KarlZeilhofer/gamearino/3d/steuerkreuz-zeik/steuerkreuz_zeik.pdf

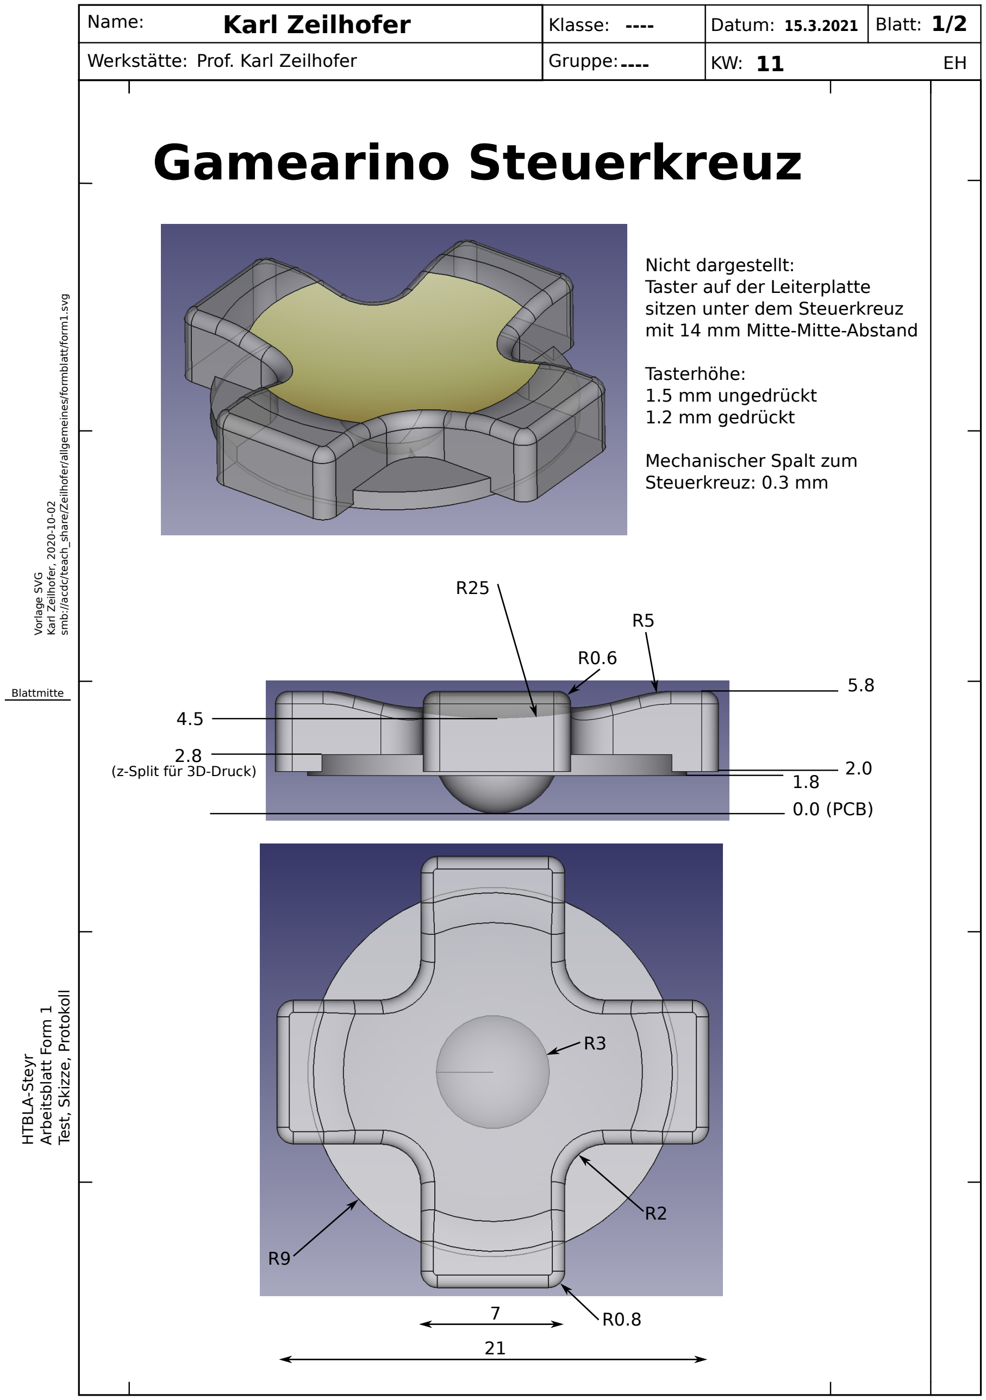
[picture p2: figure]
Werkstätte: Prof. Karl Zeilhofer; Gruppe: ----; HTBLA-Steyr; Arbeitsblatt Form 1; Test, Skizze, Protokoll; Vorlage SVG; Karl Zeilhofer, 2020-10-02; smb://acdc/teach_share/Zeilhofer/allgemeines/formblatt/form1.svg; Blattmitte; Gamearino Steuerkreuz; 0.0 (PCB); (z-Split für 3D-Druck); Nicht dargestellt: Taster auf der Leiterplatte sitzen unter dem Steuerkreuz mit 14 mm Mitte-Mitte-Abstand; Tasterhöhe: 1.5 mm ungedrückt 1.2 mm gedrückt; Mechanischer Spalt zum Steuerkreuz: 0.3 mm

Name: Karl Zeilhofer | Klasse: ---- | Datum: 15.3.2021 | 1/2 Blatt:

Name: Karl Zeilhofer | Klasse: ---- | Datum: 15.3.2021 | 2/2 Blatt:
Werkstätte: Prof. Karl Zeilhofer | Gruppe: ---- | KW: 11 EH

HTBLA-Steyr

Arbeitsblatt Form 1

Test, Skizze, Protokoll

Vorlage SVG

Karl Zeilhofer, 2020-10-02 smb://acdc/teach_share/Zeilhofer/allgemeines/formblatt/form1.svg

Blattmitte

# 3D-Druck des Steuerkreuzes

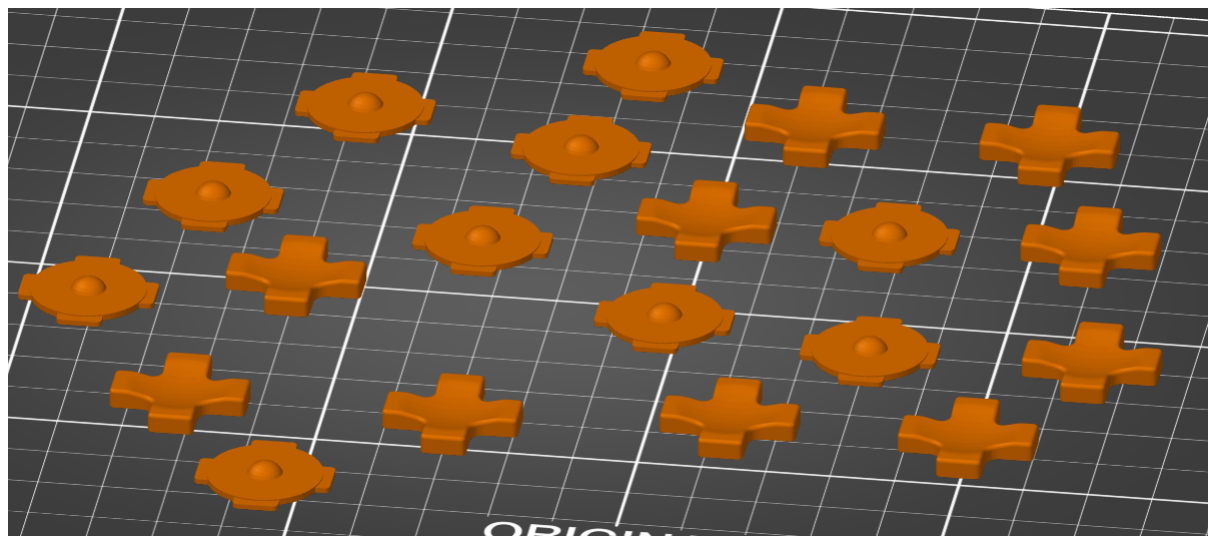
[picture p3: figure]

Das 3D-Modell wird auf Höhe 2.8 mm geteilt, um Stützstrukturen zu vermeiden, und somit saubere Oberflächen unten wie oben zu ermöglichen. Durch das Drucken vieler Teile gleichzeitig erreicht man eine bessere Qualität, da die Oberfläche der vorhergehenden Schicht Zeit bekommt, auszukühlen.

Druckmaterial: ecoPET
Drucktemperatur: 215/210 °C
Drucker: Prusa i3 MK3

Schichthöhe: 0.1 mm
