KarlZeilhofer/gamearino/3d/Screenshot from 2021-03-17 17-25-13.png

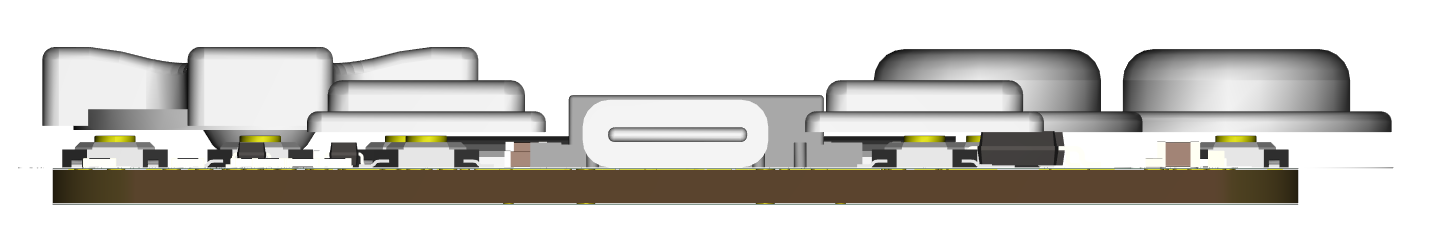
3d/Screenshot from 2021-03-17 17-25-13.png
