KarlZeilhofer/gamearino/3d/Screenshot from 2021-03-17 17-26-16.png

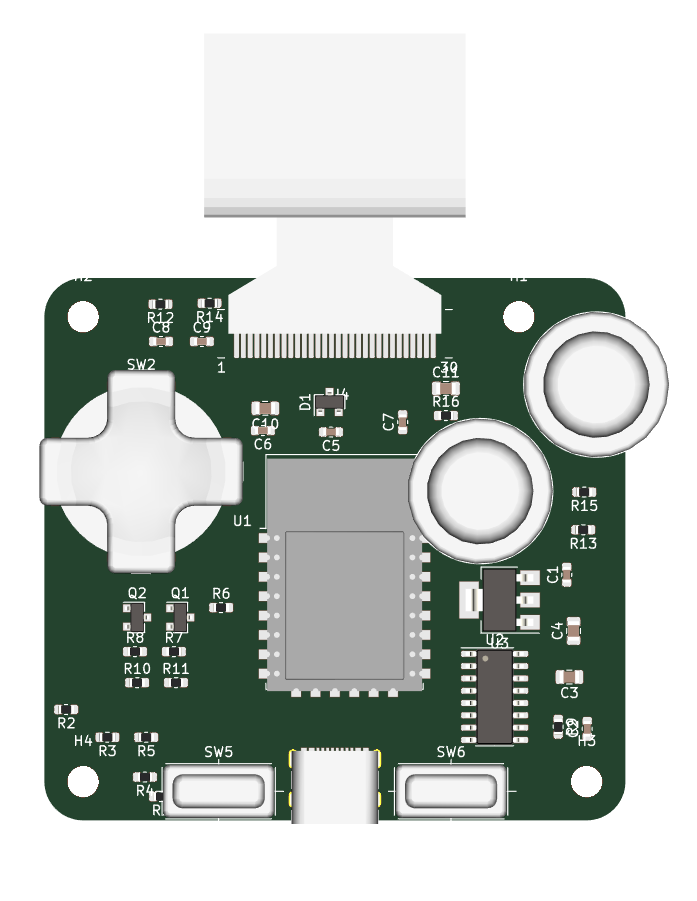
3d/Screenshot from 2021-03-17 17-26-16.png
