KarlZeilhofer/gamearino/3d/steuerkreuz-zeik/Screenshot from 2021-03-15 12-45-00.png

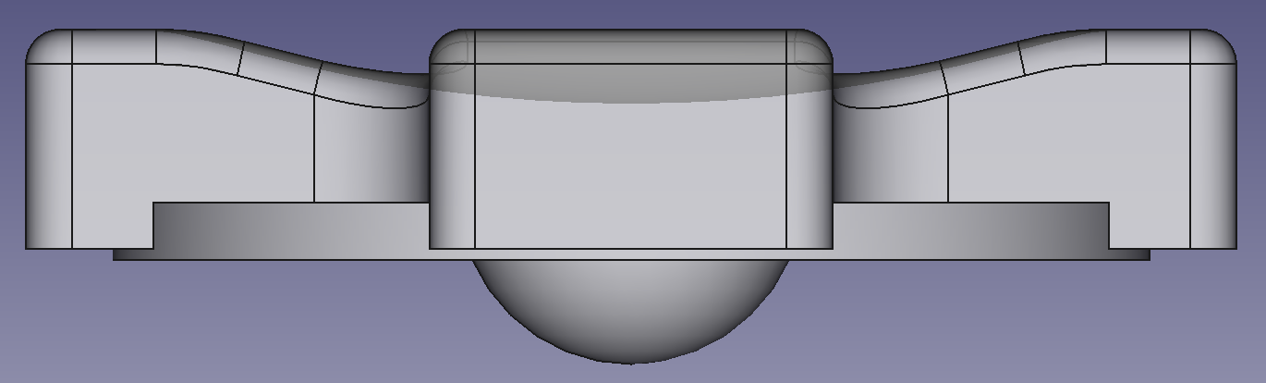
3d/steuerkreuz-zeik/Screenshot from 2021-03-15 12-45-00.png
