KarlZeilhofer/gamearino/3d/steuerkreuz-zeik/Screenshot from 2021-03-15 13-13-52.png

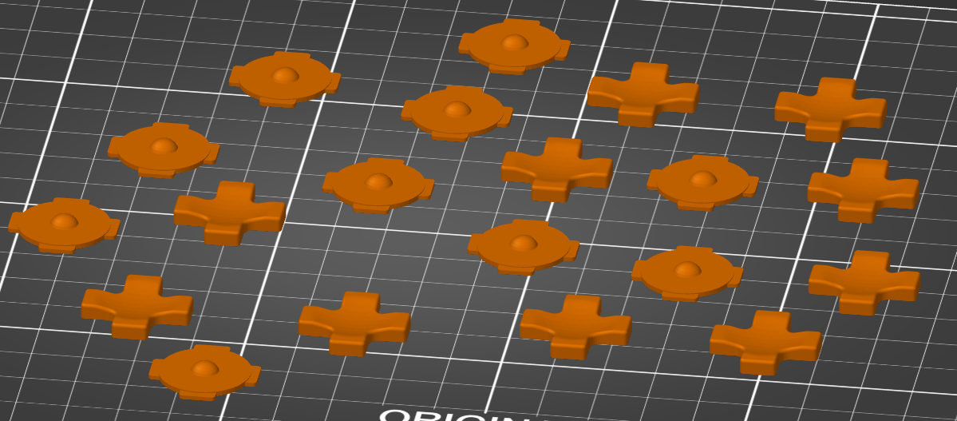
3d/steuerkreuz-zeik/Screenshot from 2021-03-15 13-13-52.png
