KarlZeilhofer/gamearino/bestellungen/2020-10-12_003.png

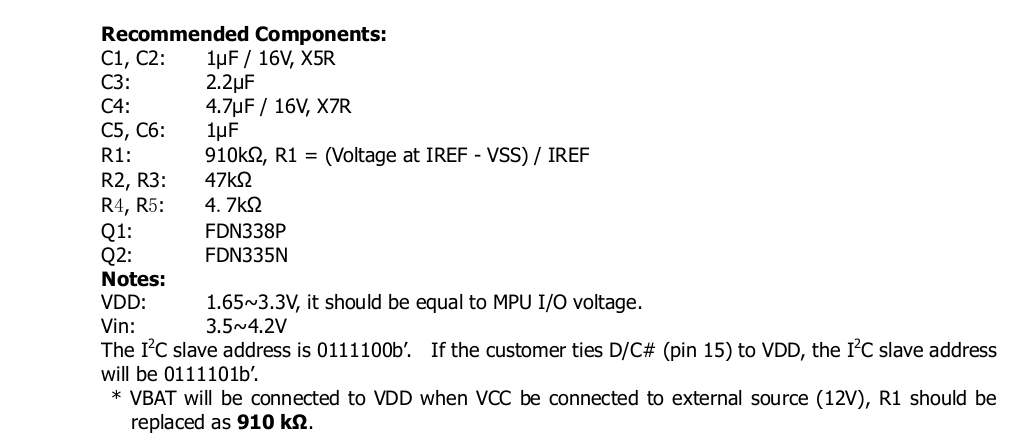
bestellungen/2020-10-12_003.png
