KarlZeilhofer/gamearino/bestellungen/2020-10-12_004.png

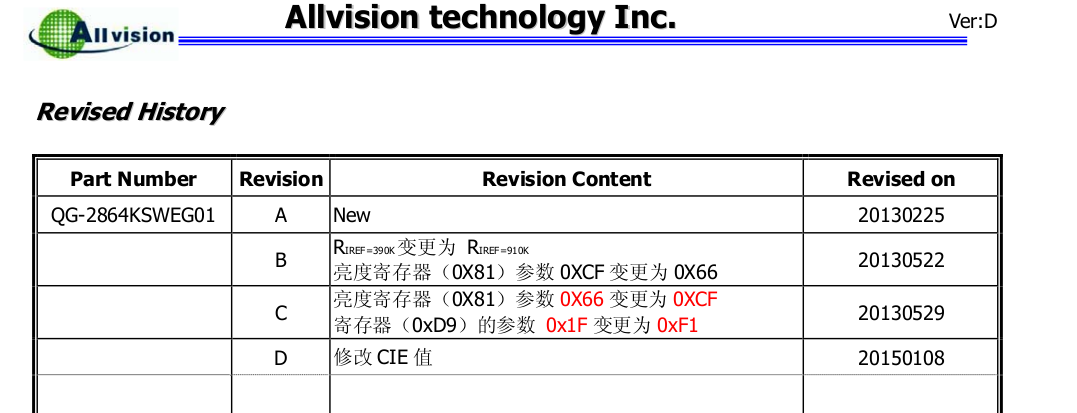
bestellungen/2020-10-12_004.png
