KarlZeilhofer/gamearino/bestellungen/2020-10-12_005.png

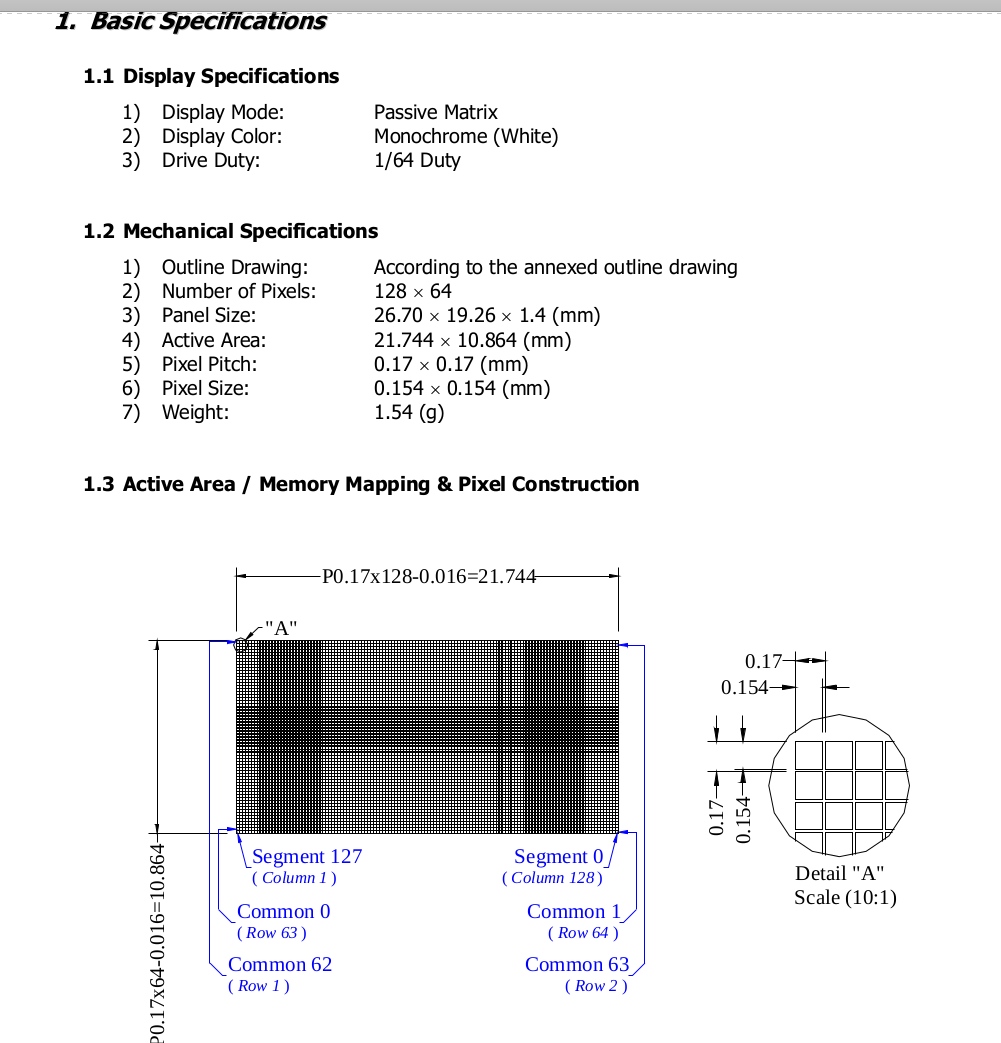
bestellungen/2020-10-12_005.png
