KarlZeilhofer/gamearino/bestellungen/2020-10-12_006.png

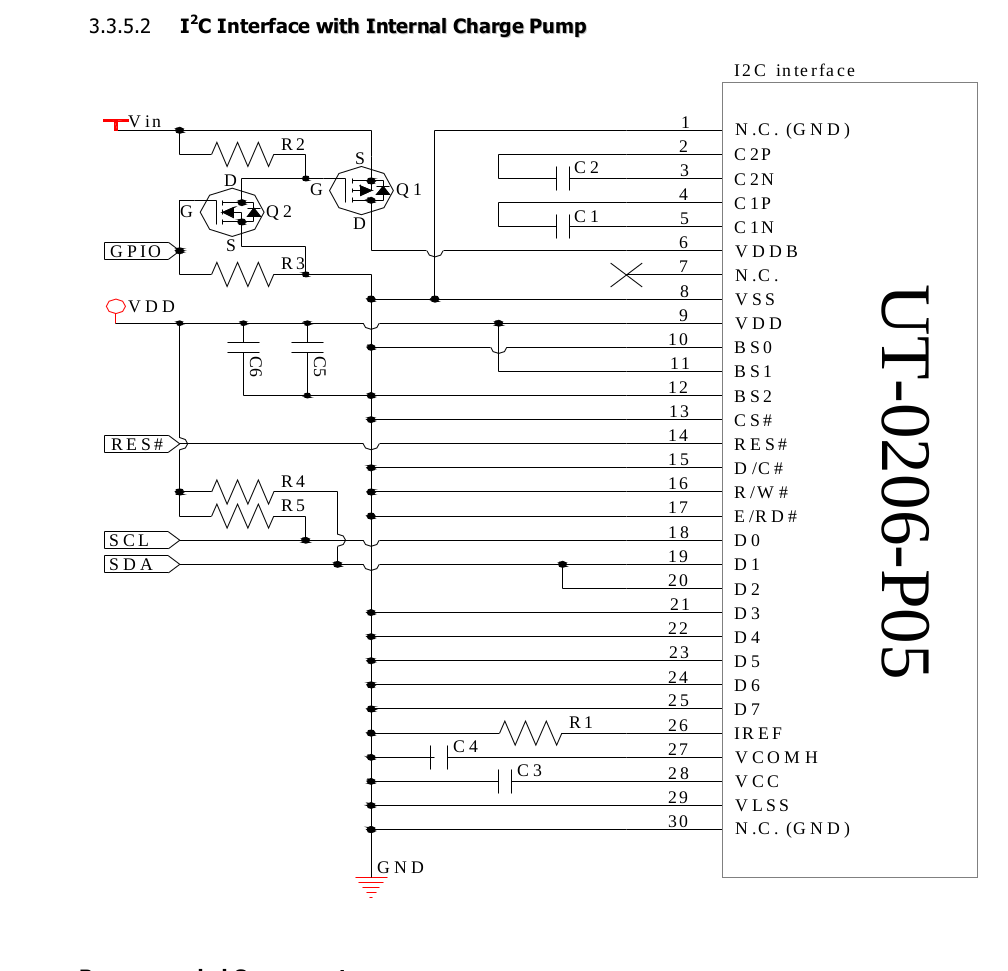
bestellungen/2020-10-12_006.png
