KarlZeilhofer/gamearino/bestellungen/2020-10-12_007.png

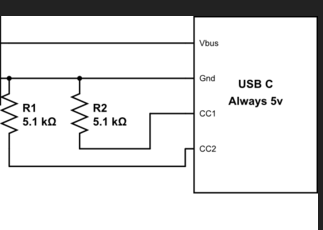
bestellungen/2020-10-12_007.png
