KarlZeilhofer/gamearino/brainstorming/2020-10-13_001.png

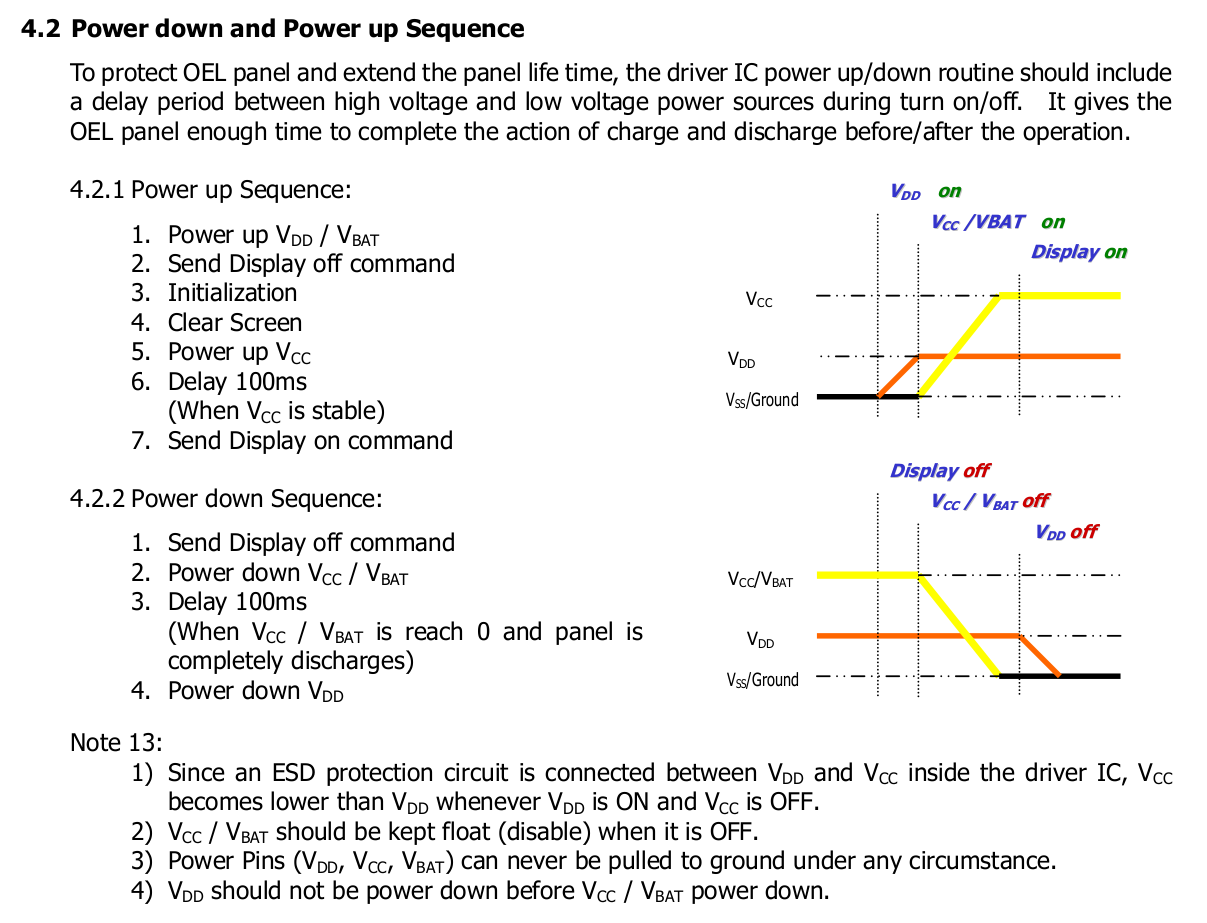
brainstorming/2020-10-13_001.png
