KarlZeilhofer/gamearino/inbetriebnahme_v0.0.2/2021-05-10_001.png

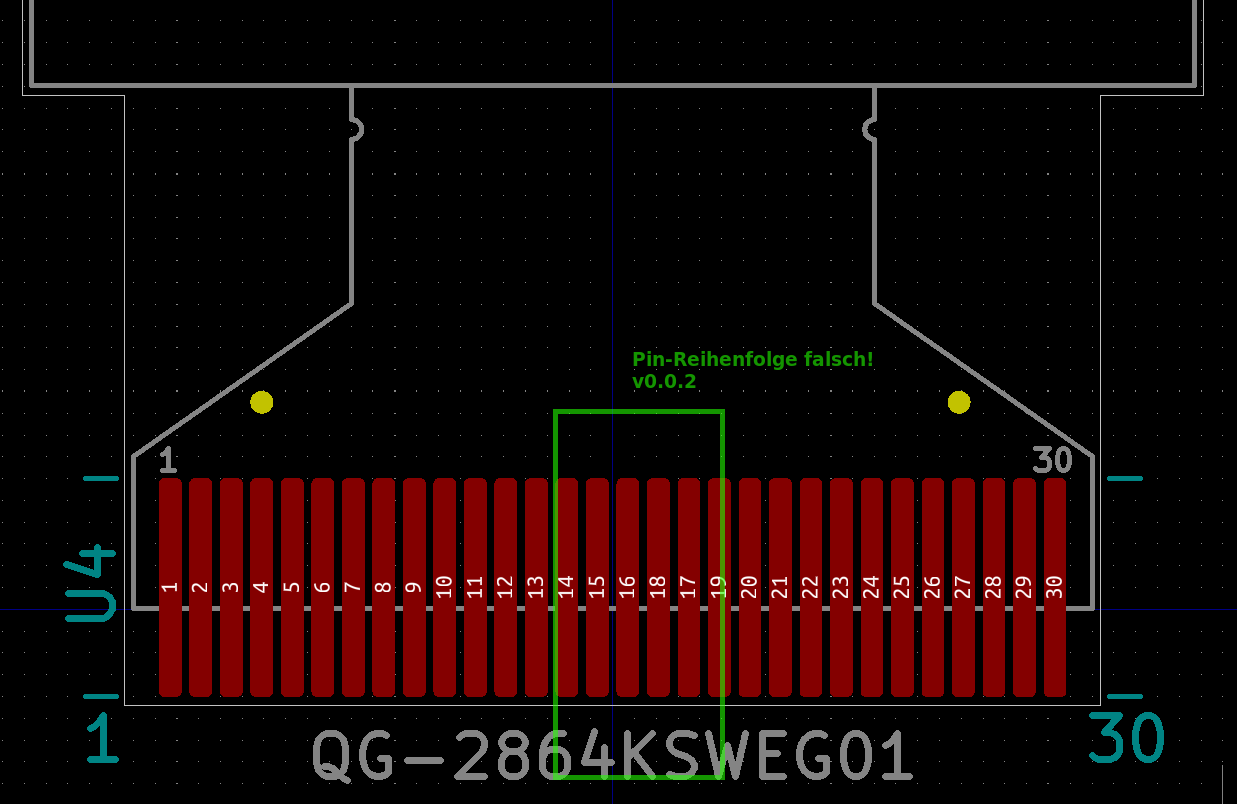
inbetriebnahme_v0.0.2/2021-05-10_001.png
