KarlZeilhofer/gamearino/kicad/screenshots/2021-04-29_012.png

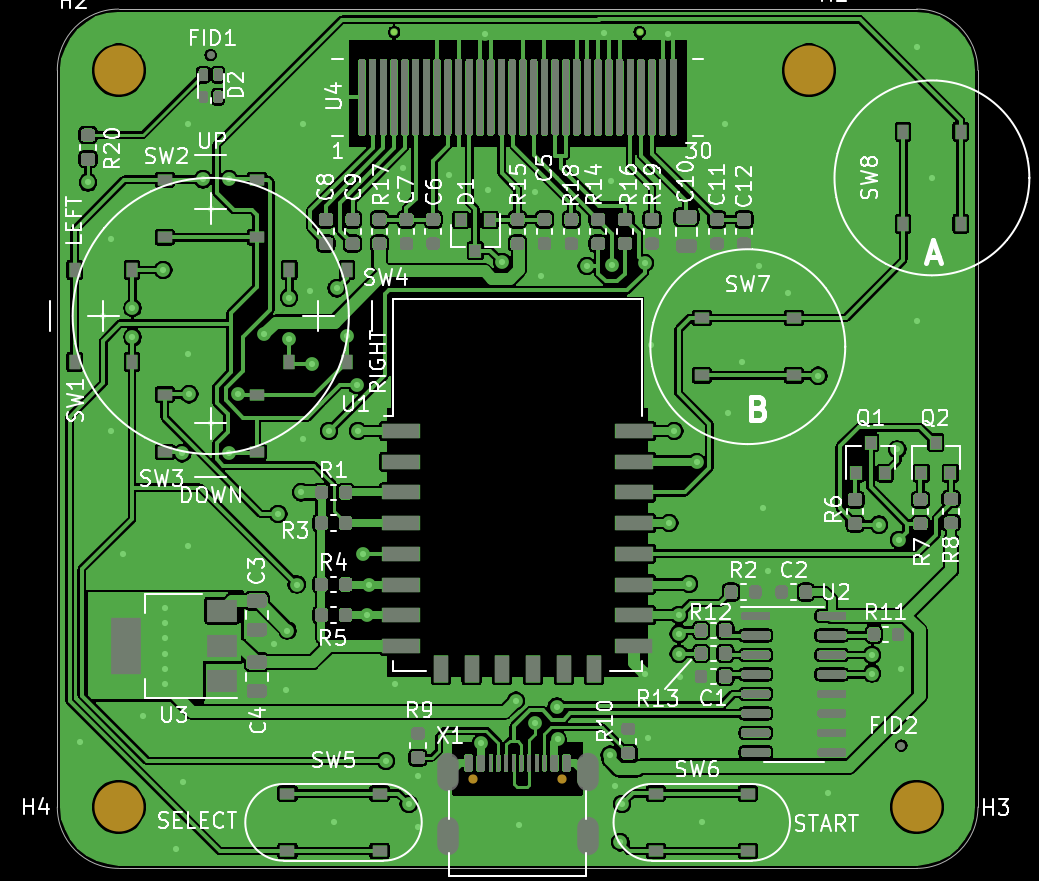
kicad/screenshots/2021-04-29_012.png
