KarlZeilhofer/gamearino/kicad/screenshots/2021-04-29_013.png

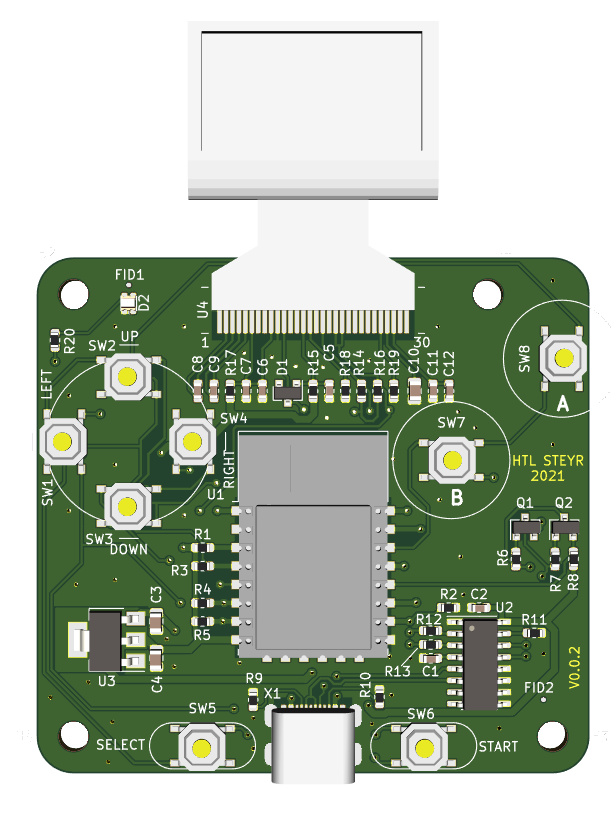
kicad/screenshots/2021-04-29_013.png
