KarlZeilhofer/gamearino/kicad/screenshots/2021-04-29_014.png

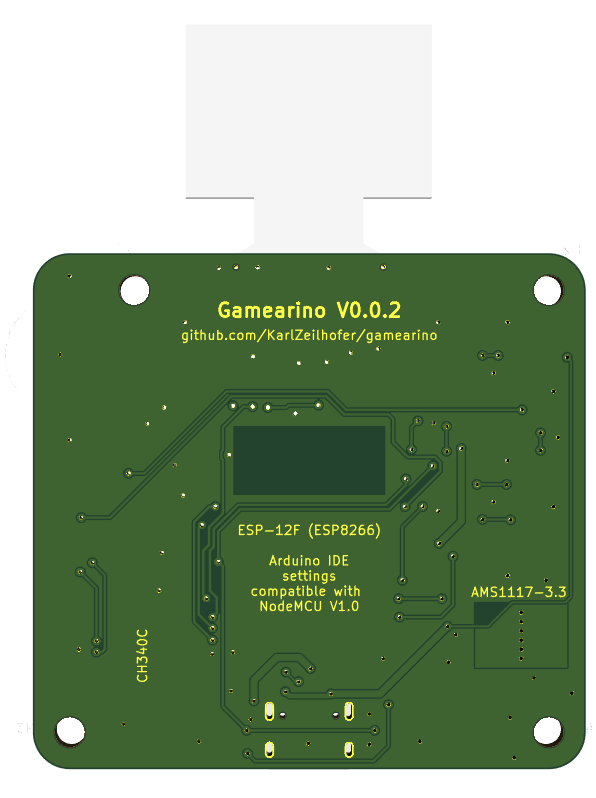
kicad/screenshots/2021-04-29_014.png
