KarlZeilhofer/gamearino/kicad/screenshots/2021-04-29_015.png

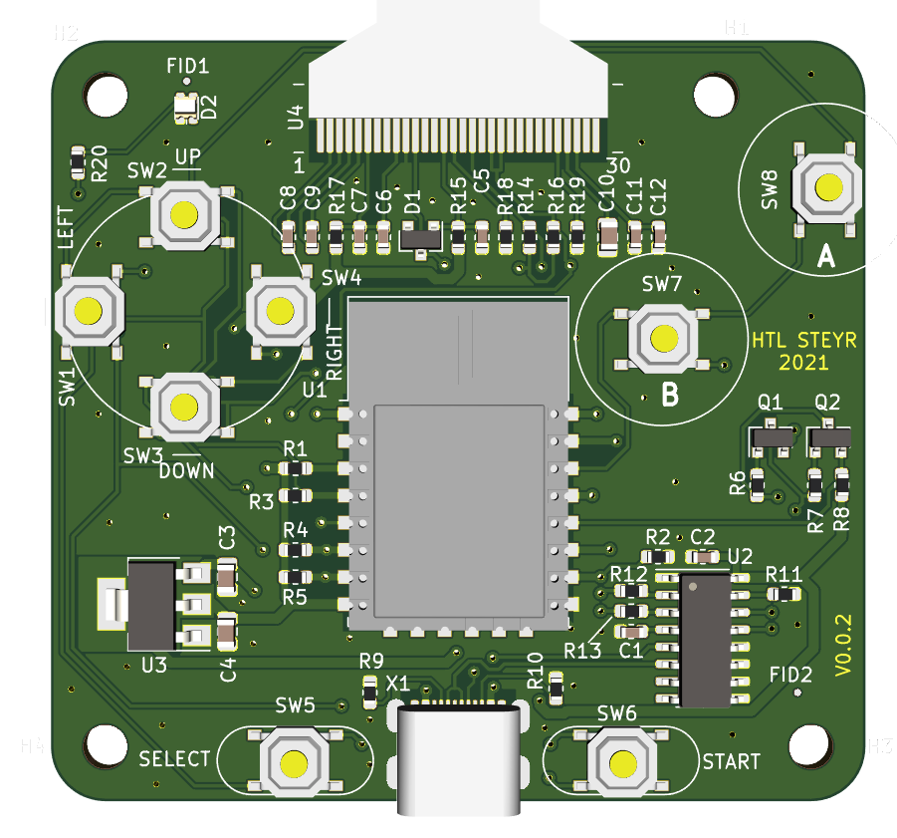
kicad/screenshots/2021-04-29_015.png
