KarlZeilhofer/gamearino/kicad/screenshots/2021-04-29_016.png

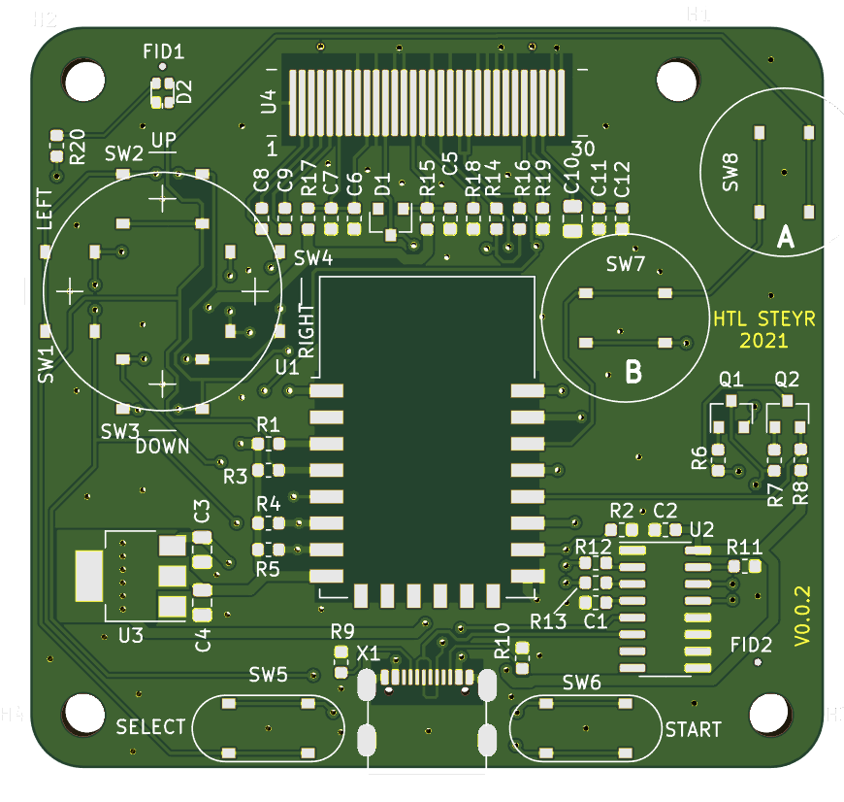
kicad/screenshots/2021-04-29_016.png
