KarlZeilhofer/gamearino/kicad/screenshots/2021-04-29_017.png

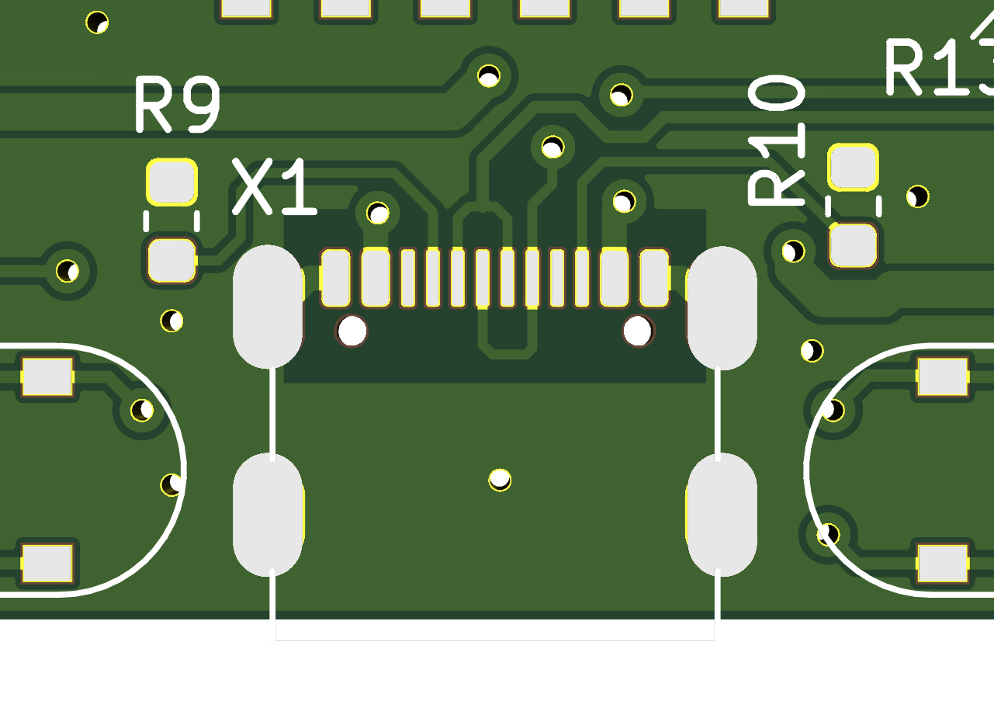
kicad/screenshots/2021-04-29_017.png
