KarlZeilhofer/gamearino/kicad/screenshots/2021-04-29_018.png

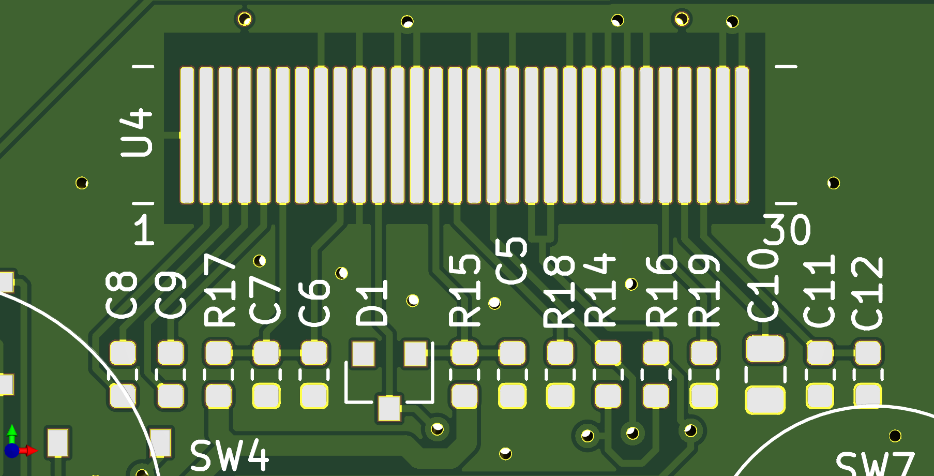
kicad/screenshots/2021-04-29_018.png
