KarlZeilhofer/gamearino/kicad/screenshots/2021-04-29_019.png

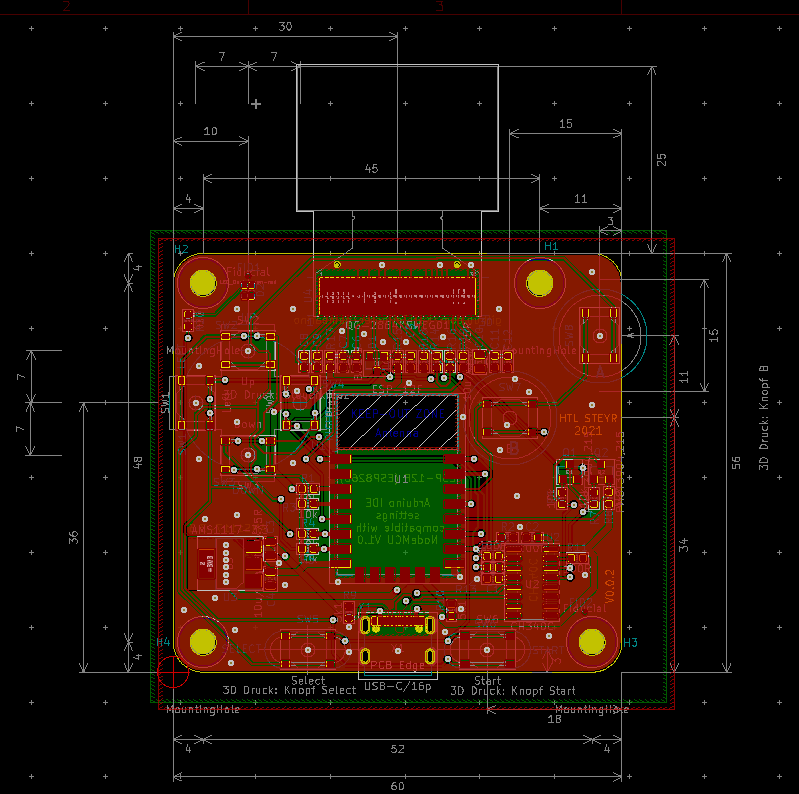
kicad/screenshots/2021-04-29_019.png
