KarlZeilhofer/gamearino/3d/gehäuse/gamearino-steuerkreuz_v2.stl

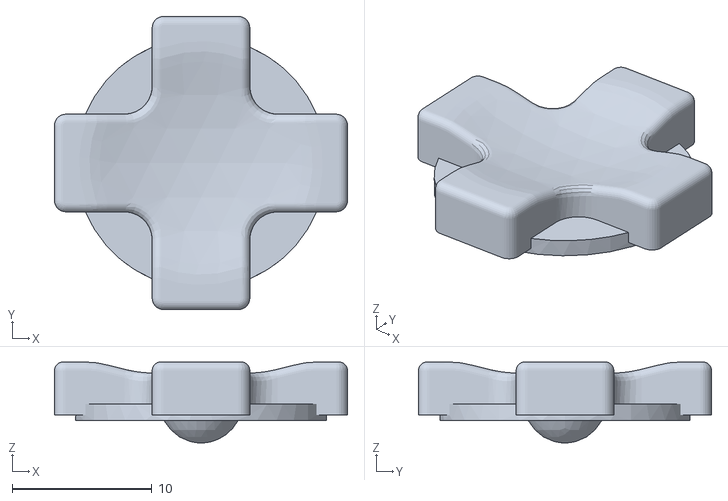
[picture p46: CAD file, 2021-04-21]
3d/gehäuse/gamearino-steuerkreuz_v2.stl
21.0 x 21.0 x 5.80
