KarlZeilhofer/gamearino/3d/gehäuse/gamearino-deckel_v0.1.stl

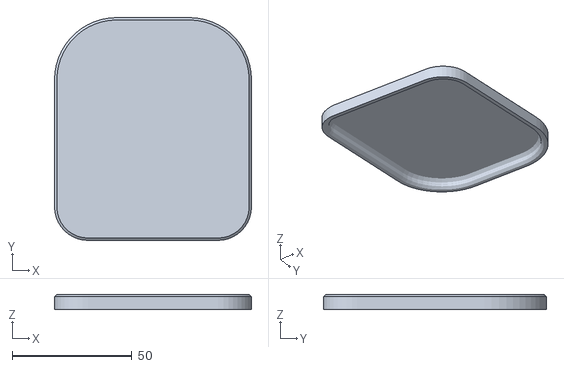
[picture p47: CAD file, 2021-04-21, an earlier design]
3d/gehäuse/gamearino-deckel_v0.1.stl
82.4 x 93.2 x 6.40
