KarlZeilhofer/gamearino/kicad/sch/gamearino.pdf

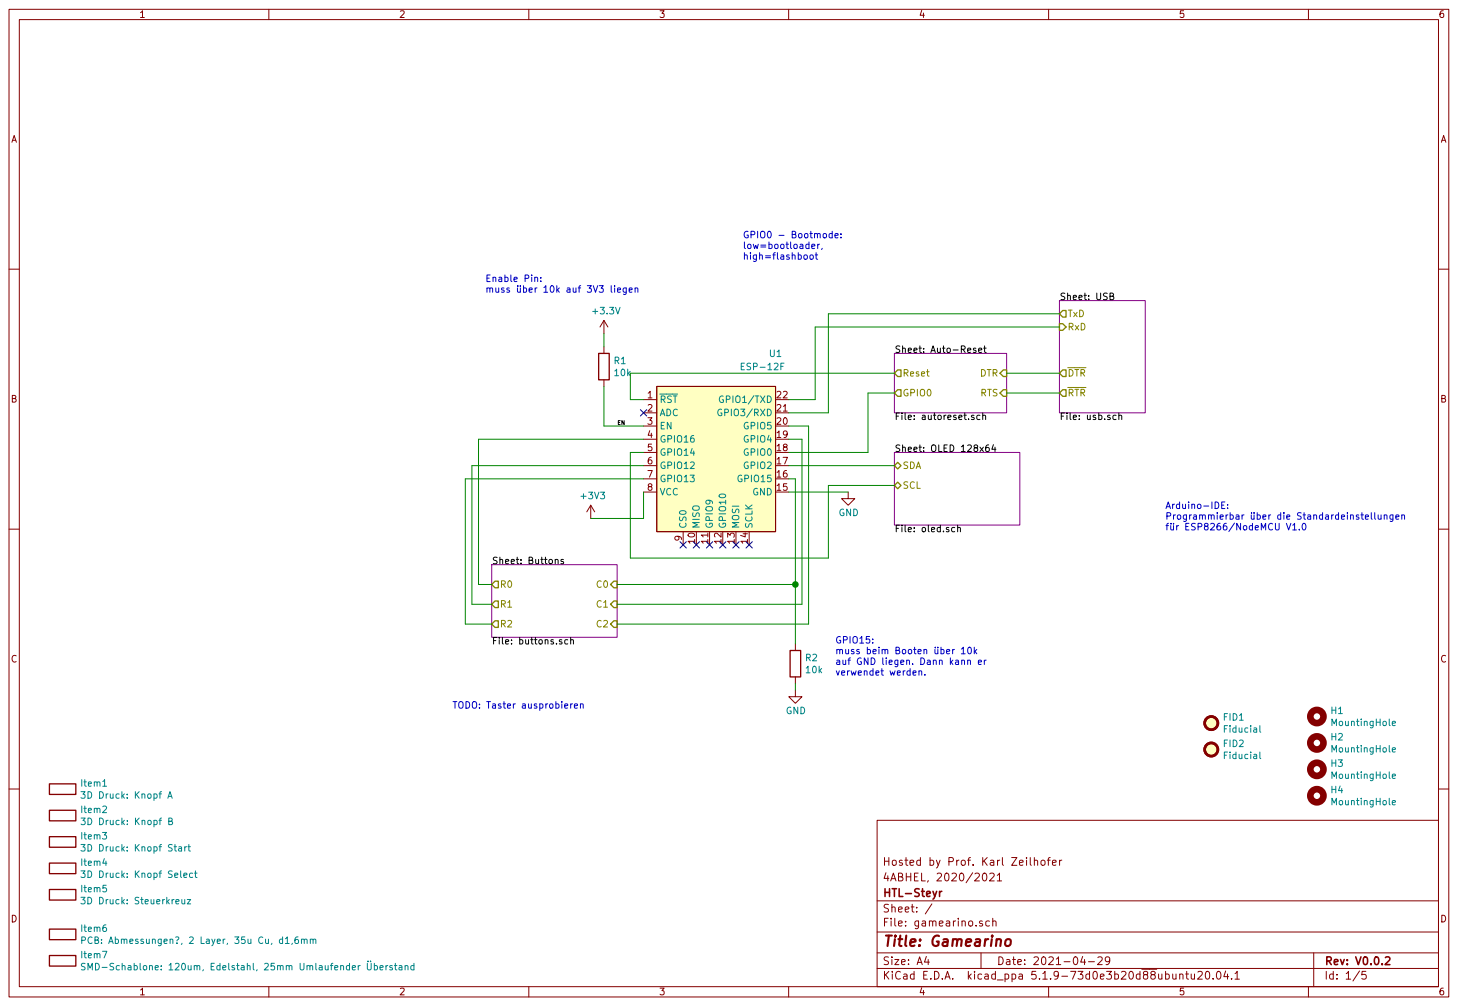
[picture p49: page 1]

Hosted by Prof. Karl Zeilhofer Sheet: OLED 128x64 File: oled.sch SDA

für ESP8266/NodeMCU V1.0 GPIO15: muss beim Booten über 10k auf GND liegen. Dann kann er verwendet werden. Enable Pin: muss über 10k auf 3V3 liegen

Sheet: USB
File: usb.sch TxD
RxD

FID1 Fiducial Item7SMD-Schablone: 120um, Edelstahl, 25mm Umlaufender Überstand

4ABHEL, 2020/2021
File: gamearino.sch Sheet: / HTL-Steyr

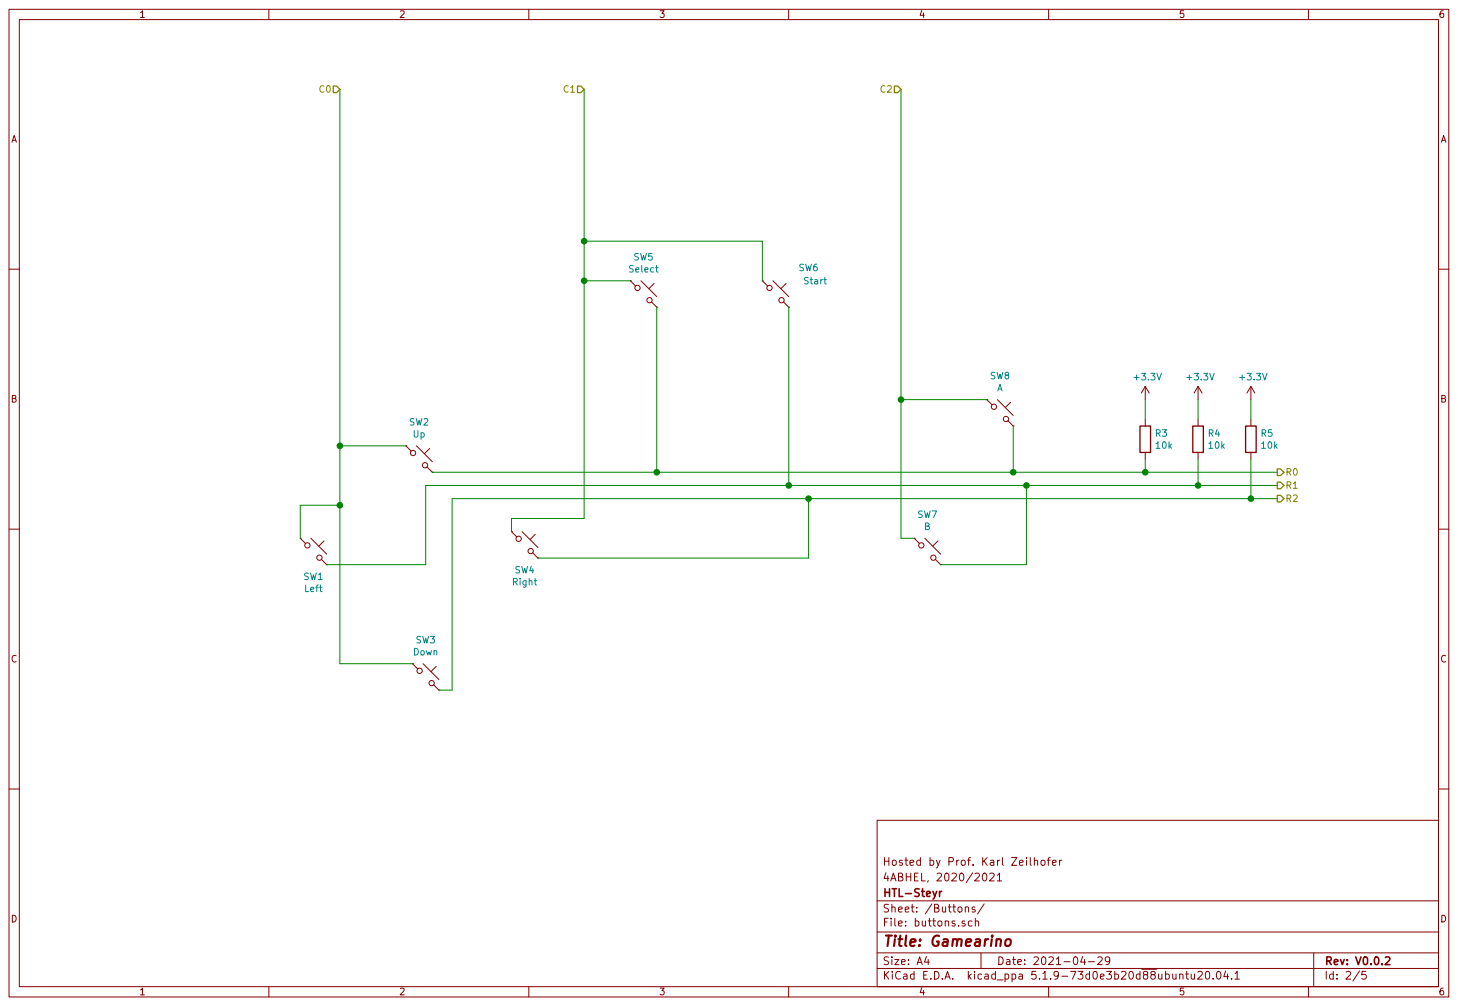
[picture p50: page 2]

Hosted by Prof. Karl Zeilhofer SW1

4ABHEL, 2020/2021
File: buttons.sch Sheet: /Buttons/ HTL-Steyr

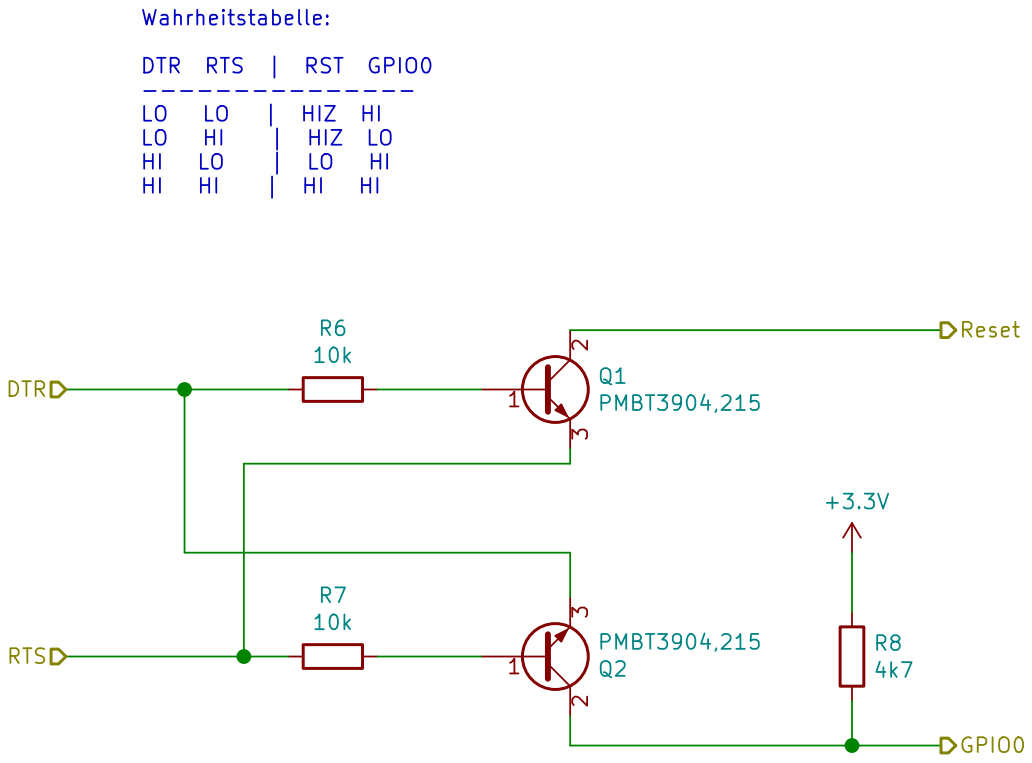
[picture p51: page 3]

--------------- LO LO | HIZ HI

Hosted by Prof. Karl Zeilhofer
4ABHEL, 2020/2021
File: autoreset.sch Sheet: /Auto-Reset/ HTL-Steyr

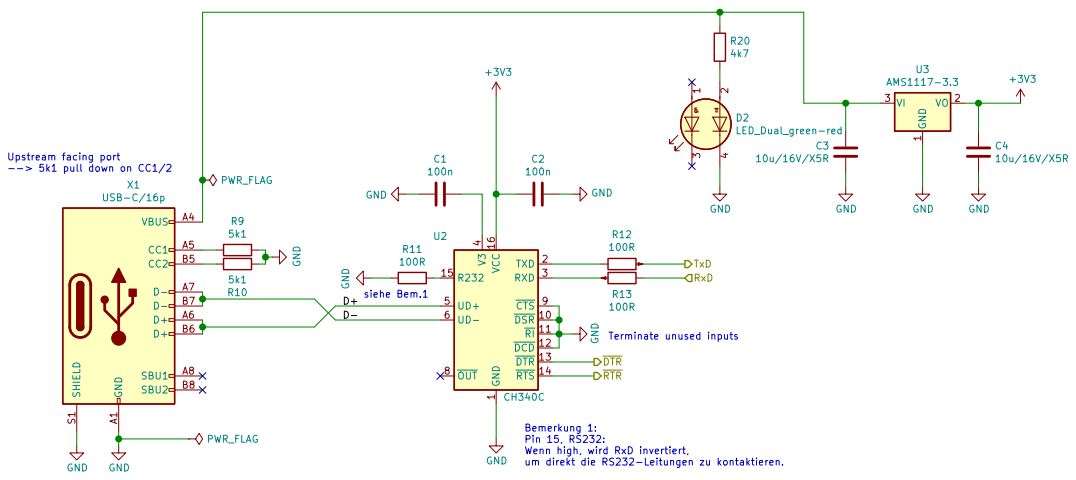
[picture p52: page 4]

4 UD+ 5 UD- 6 OUT 8 CTS 9 U2 CH340C

1 DSR 10 RI 11 DCD 12 DTR 13 RTS 14 R232 15 VCC 16 TXD 2 RXD 3 V3

um direkt die RS232-Leitungen zu kontaktieren.

Hosted by Prof. Karl Zeilhofer
4ABHEL, 2020/2021
File: usb.sch Sheet: /USB/ HTL-Steyr

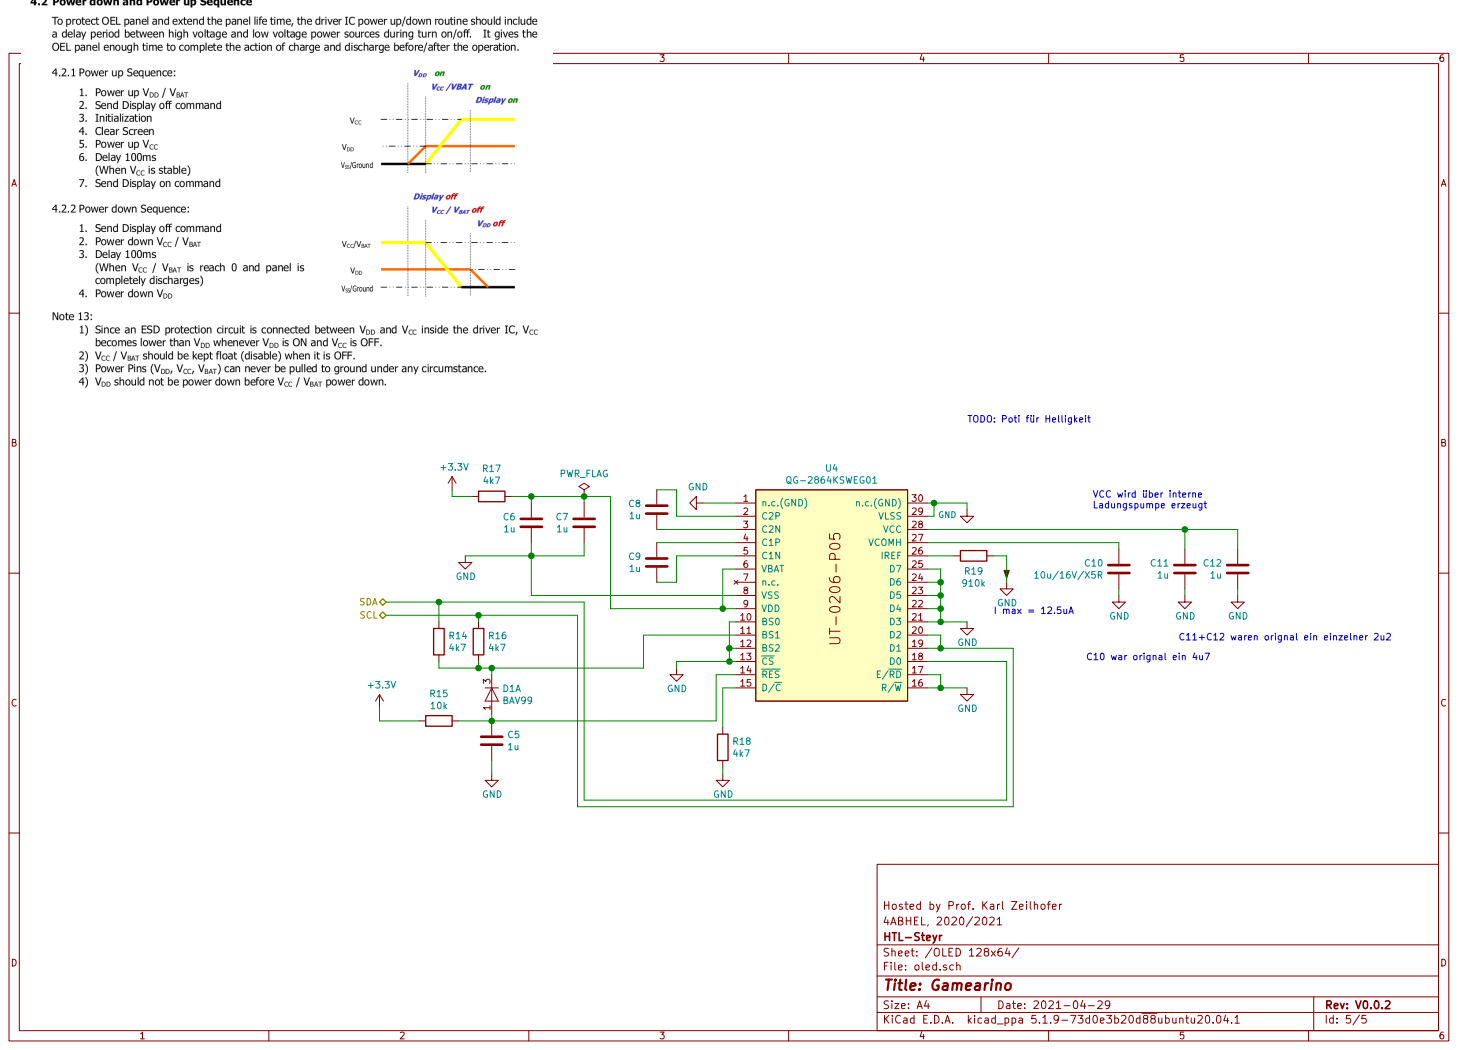
[picture p53: page 5]

Hosted by Prof. Karl Zeilhofer C5

4ABHEL, 2020/2021
File: oled.sch Sheet: /OLED 128x64/ HTL-Steyr
